BEEMB/Battery-Health-Monitor/Documentation/Images/Assembled Housing.jpg

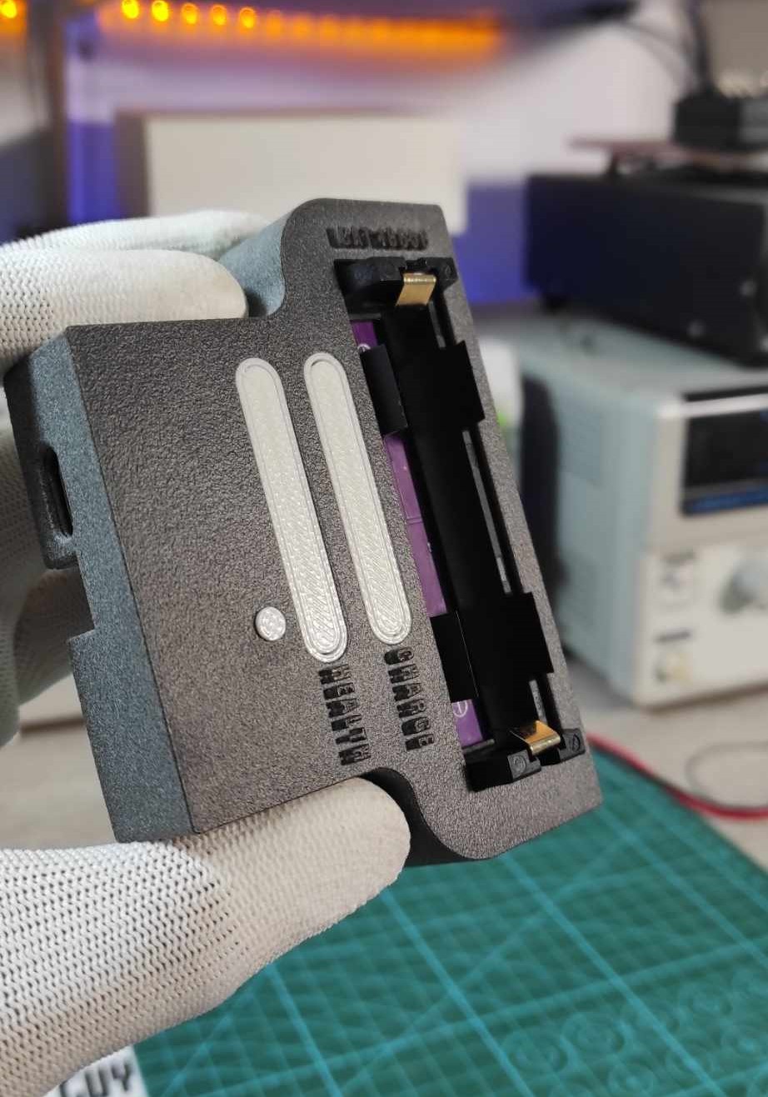
Documentation/Images/Assembled Housing.jpg
