BEEMB/Battery-Health-Monitor/Documentation/Images/Final PCB Assembly.jpg

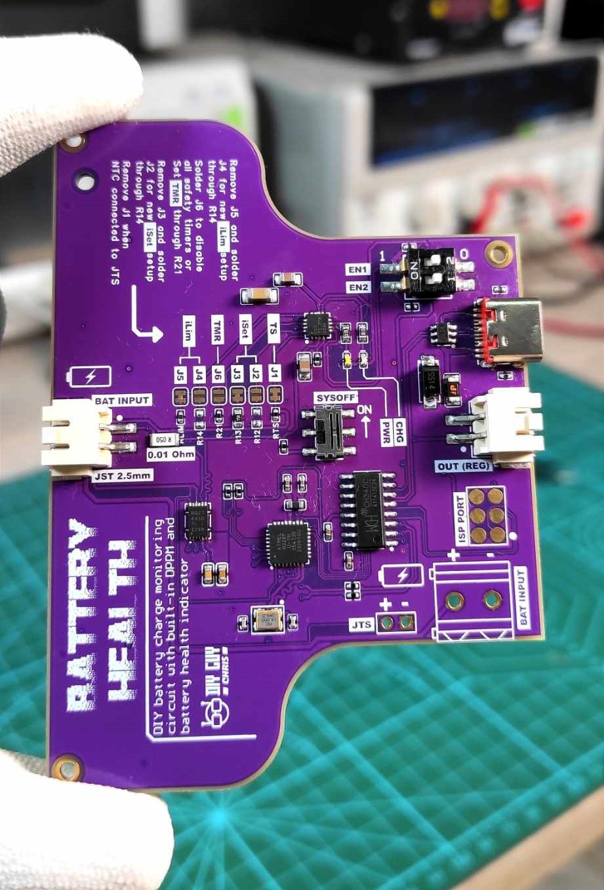
Documentation/Images/Final PCB Assembly.jpg
