BEEMB/Battery-Health-Monitor/Documentation/Images/Soldering inspection.jpg

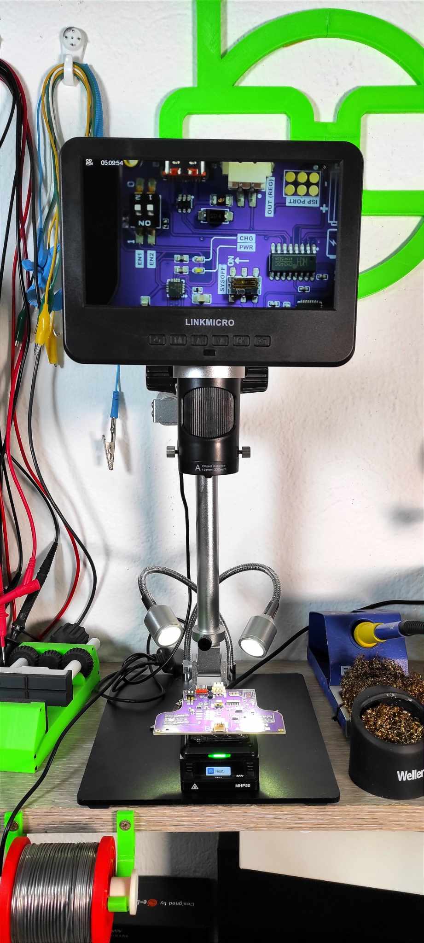
Documentation/Images/Soldering inspection.jpg
