BEEMB/Battery-Health-Monitor/Documentation/Images/Power test.jpg

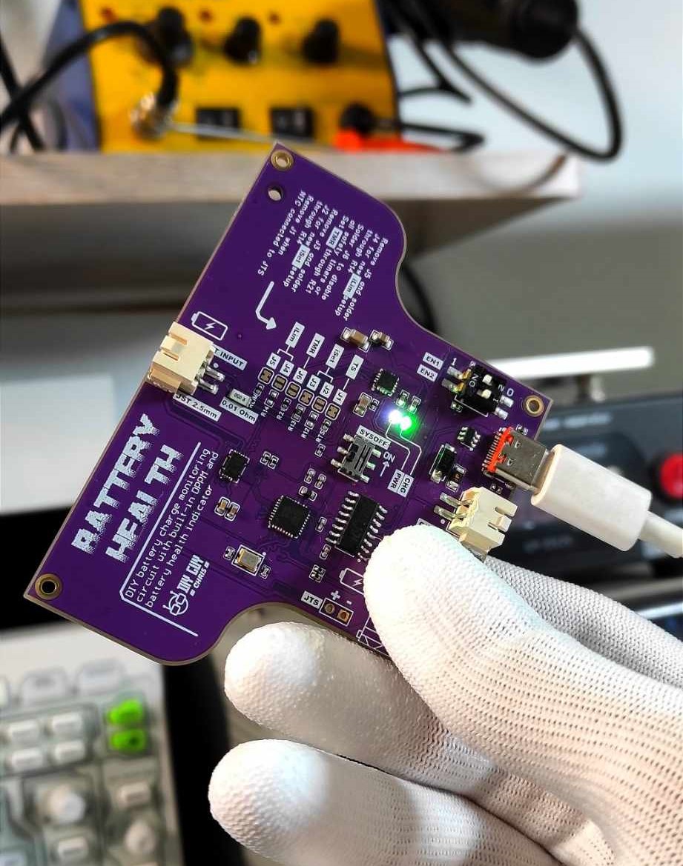
Documentation/Images/Power test.jpg
